panbachi/wordclock/wordclock/src/controller.cpp

#include <ArduinoJson.h>

#include "config.h"
#include "grid.h"
#include "controller.h"
#include "httpServer.h"
#include "color.h"
#include "gui.h"
#include "wifi.h"
#include "time.h"
#include "led.h"
#include "utcOffset.h"

void Controller::index() {
  String content = Gui::index();

  HttpServer::web.sendHeader("Location", "http://" + HttpServer::ip);
  HttpServer::web.send(200, "text/html", content);
}

void Controller::saveColor() {
  String json = HttpServer::web.arg("plain");

  DynamicJsonDocument doc(2048);
  deserializeJson(doc, json);

  Config::color_fg = Color::hexToRgb(doc["fg"].as<String>());
  Config::color_bg = Color::hexToRgb(doc["bg"].as<String>());
  Config::power_supply = doc["power_supply"].as<int>();
  Config::brightness =
    (doc["brightness"].as<double>() > Led::getMaxBrightnessPercnt()) ? Led::getMaxBrightnessPercnt() : doc["brightness"].as<double>();

  Config::healthcheck = doc["healthcheck"].as<int>() == 1;

  Config::save();
  Grid::setTime(Time::hour, Time::minute);

  HttpServer::web.send(200, "text/html", "");
}

void Controller::saveTime() {
  String json = HttpServer::web.arg("plain");

  DynamicJsonDocument doc(2048);
  deserializeJson(doc, json);

  Config::automatic_timezone = doc["tz_auto"].as<int>() == 1;

  // store the last known value anyway.
  Config::timezone = doc["tz"].as<int>();

  if (Config::automatic_timezone) {
    UtcOffset::updateLocalizedUtcOffset();
  }

  Config::ntp = doc["ntp"].as<String>();

  Config::save();
  Grid::setTime(Time::hour, Time::minute);

  HttpServer::web.send(200, "text/html", "");
}

void Controller::saveDnd() {
  String json = HttpServer::web.arg("plain");

  DynamicJsonDocument doc(2048);
  deserializeJson(doc, json);


  Config::dnd_active = doc["dnd_active"].as<int>() == 1;
  Config::dnd_start.hour = doc["dnd_start_hour"].as<int>();
  Config::dnd_start.minute = doc["dnd_start_minute"].as<int>();
  Config::dnd_end.hour = doc["dnd_end_hour"].as<int>();
  Config::dnd_end.minute = doc["dnd_end_minute"].as<int>();

  Config::save();
  Grid::setTime(Time::hour, Time::minute);

  HttpServer::web.send(200, "text/html", "");
}

void Controller::deleteWiFi() {
  Wifi::reset();
  ESP.restart();
  HttpServer::web.send(200, "text/html", "");
}

void Controller::getLogoSvg() {
  String content = "<?xml version=\"1.0\" encoding=\"UTF-8\"?><svg width=\"1024\" height=\"1024\" version=\"1.1\" viewBox=\"0 0 270.93 270.93\" xmlns=\"http://www.w3.org/2000/svg\"><rect x=\".13216\" y=\".13216\" width=\"270.67\" height=\"270.67\" rx=\"26.433\" ry=\"26.433\" fill=\"#333\"/><rect x=\"15.992\" y=\"15.992\" width=\"238.95\" height=\"238.95\" rx=\"23.335\" ry=\"23.335\" fill=\"#eee\"/><g fill=\"#3d72a8\"><circle cx=\"90.488\" cy=\"50.271\" r=\"13.098\"/><circle cx=\"47.096\" cy=\"50.271\" r=\"13.098\"/><circle cx=\"90.488\" cy=\"93.662\" r=\"13.098\"/><circle cx=\"133.88\" cy=\"93.662\" r=\"13.098\"/><circle cx=\"177.4\" cy=\"93.662\" r=\"13.098\"/><circle cx=\"133.88\" cy=\"180.45\" r=\"13.098\"/><circle cx=\"177.4\" cy=\"180.45\" r=\"13.098\"/><circle cx=\"220.79\" cy=\"180.45\" r=\"13.098\"/><circle cx=\"47.096\" cy=\"180.45\" r=\"13.098\"/></g></svg>";

  HttpServer::web.send(200, "image/svg+xml", content);
}

void Controller::getManifest() {
  String content = "";

  content += "{";
  content += "\"background_color\": \"#FFFFFF\",";
  content += "\"description\": \"panbachi.de WordClock\",";
  content += "\"dir\": \"ltr\",";
  content += "\"display\": \"standalone\",";
  content += "\"icons\": [{\"sizes\": \"128x128\", \"src\": \"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", \"type\": \"image/png\"}],";
  content += "\"lang\": \"en-US\",";
  content += "\"name\": \"panbachi.de WordClock\",";
  content += "\"short_name\": \"WordClock\",";
  content += "\"start_url\": \"/\",";
  content += "\"theme_color\": \"#3d72a8\"";
  content += "}";

  HttpServer::web.send(200, "application/json", content);
}

void Controller::notFound() {
  if(HttpServer::web.method() == HTTP_OPTIONS) {
    HttpServer::web.sendHeader("Allow", "DELETE,GET,HEAD,OPTIONS,POST,PUT");
    HttpServer::web.send(200, "text/html", "");

    return;
  }

  HttpServer::web.send(404, "text/html", "NOT FOUND");
}
