panbachi/wordclock/wordclock/src/controller.h

#ifndef WORDCLOCK_CONTROLLER_H
#define WORDCLOCK_CONTROLLER_H

class Controller {
  public:
    static void index();
    static void saveColor();    
    static void saveTime();    
    static void saveDnd();    
    static void deleteWiFi();
    static void getLogoSvg();
    static void getManifest();
    static void notFound();
};

#endif
