panbachi/wordclock/wordclock/src/led.cpp

#include <FastLED.h>

#include "grid.h"
#include "led.h"
#include "config.h"

int Led::getLedId(int id) {
  int col = id % GRID_COLS;
  int row = (floor)(id / GRID_COLS);
  int led = 0;

  if(GRID_FIRST == 3) {
    led = (row % 2 != GRID_ROWS % 2) ? (GRID_ROWS - row) * GRID_COLS - 1 - col : (GRID_ROWS - row - 1) * GRID_COLS + col;
  } else if(GRID_FIRST == 2) {
    led = (row % 2 == GRID_ROWS % 2) ? (GRID_ROWS - row) * GRID_COLS - 1 - col : (GRID_ROWS - row - 1) * GRID_COLS + col;
  } else if(GRID_FIRST == 1) {
    led = (row % 2 == 0) ? ((row * GRID_COLS) + col) : ((row + 1) * GRID_COLS) - col - 1;
  } else if(GRID_FIRST == 0) {
    led = (row % 2 == 1) ? ((row * GRID_COLS) + col) : ((row + 1) * GRID_COLS) - col - 1;
  }

  if(GRID_SINGLE_MINUTES == 0) {
    led += EXTRA_LEDS;
  }

  return led;
}

void Led::setup() {
  FastLED.addLeds<NEOPIXEL, DATA_PIN>(Led::ids, NUM_LEDS);
  FastLED.setBrightness(50);

  for(int i = 0; i < NUM_LEDS; i++) {
    Led::ids[i].setRGB(0, 0, 0);
  }

  FastLED.show();
}

double Led::getMaxBrightnessPercnt() {
  const int max_consumption = getMaxNumberIlluminatedLeds() * CONSUMPTION_PER_LED;
  const double brightness_percnt = (Config::power_supply - CONSUMPTION_D1_MINI) / (double) max_consumption;

  return (brightness_percnt >= 1.0) ? 1.0 : brightness_percnt;
}

int Led::getMaxNumberIlluminatedLeds() {

  int max_time_it_is = sizeof(Grid::time_it_is)/sizeof(Grid::time_it_is[0]);
  int max_time_minutes = sizeof(Grid::time_minutes[0])/sizeof(Grid::time_minutes[0][0]);
  int max_time_hours = sizeof(Grid::time_hours[0])/sizeof(Grid::time_hours[0][0]);

  return max_time_it_is + max_time_minutes + max_time_hours;
}

CRGB Led::ids[NUM_LEDS];
